fumyskin/TRIDANT_project/plots/batch1/GNSS_01.png

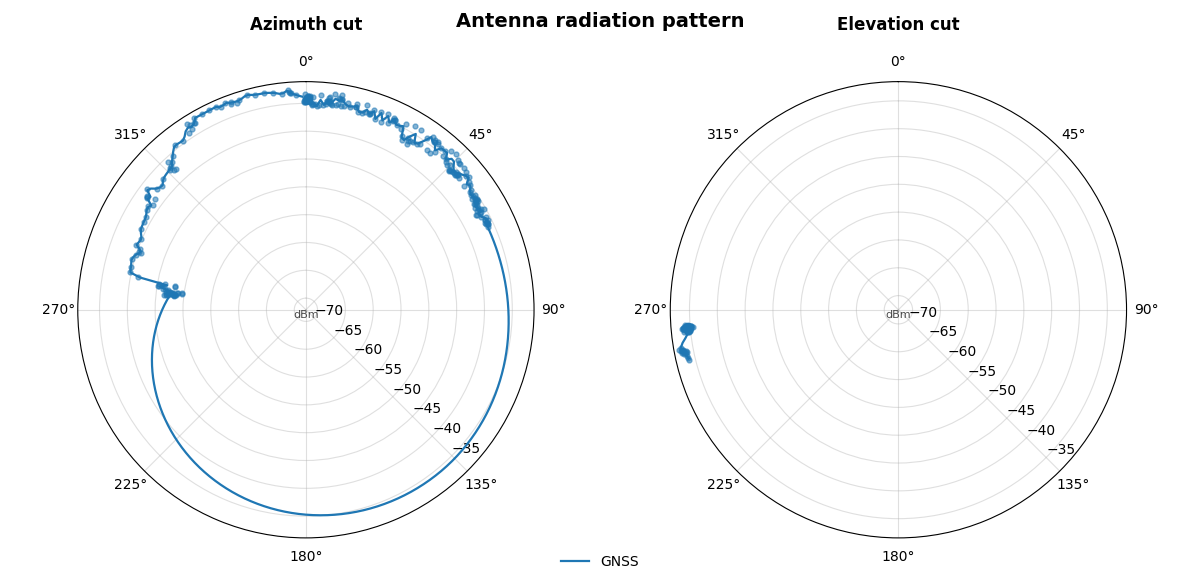
plots/batch1/GNSS_01.png
