fumyskin/TRIDANT_project/plots/batch1/GNSS_01_nhc.png

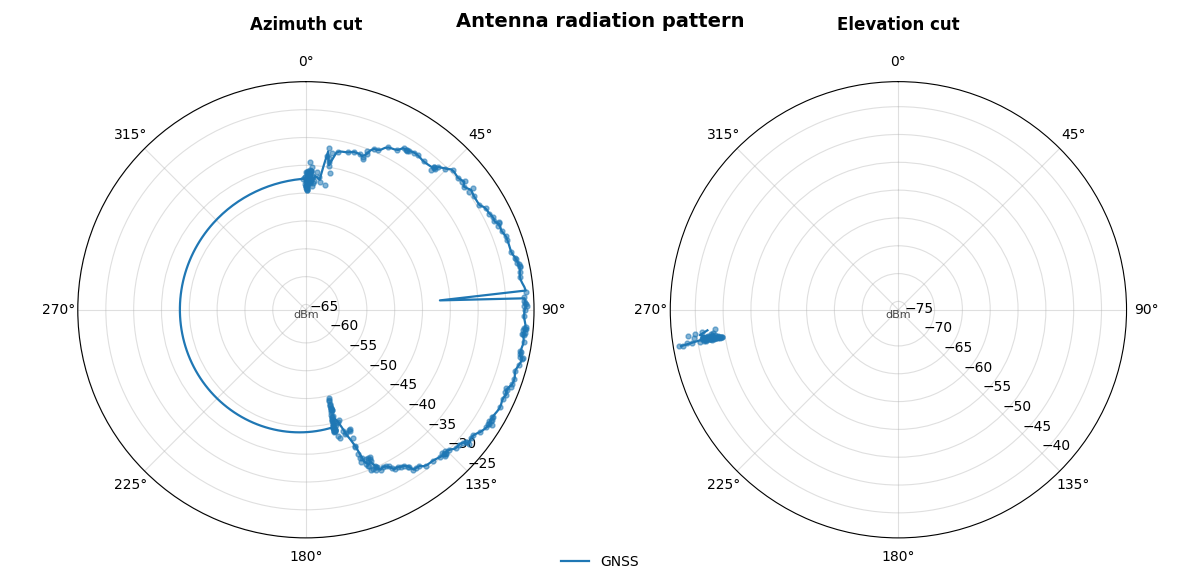
plots/batch1/GNSS_01_nhc.png
