fumyskin/TRIDANT_project/plots/batch1/GNSS_03_nhc_elevation.png

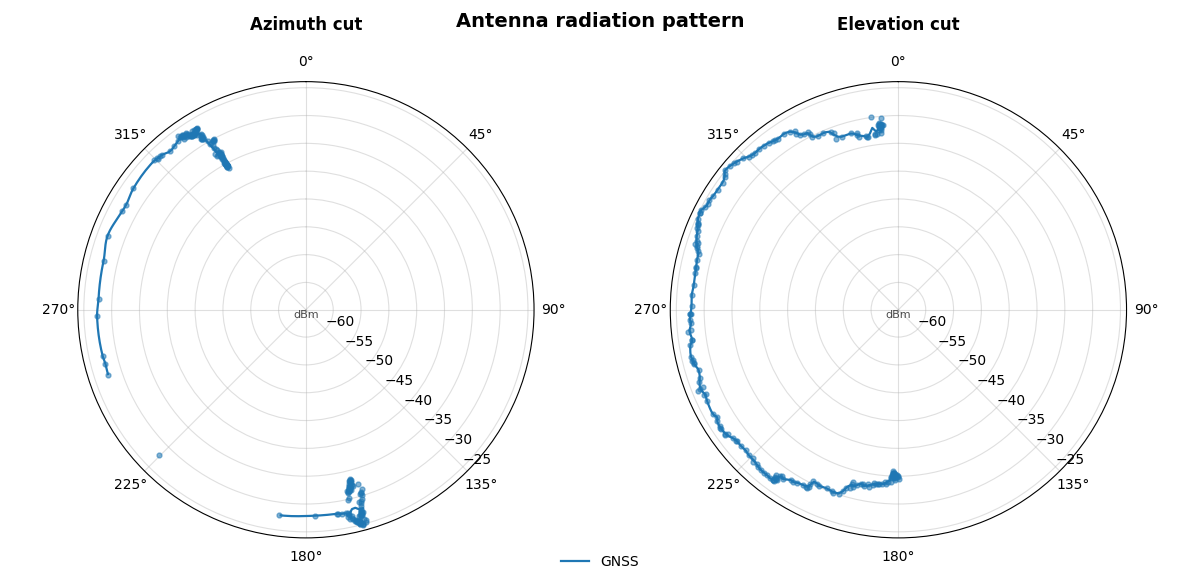
plots/batch1/GNSS_03_nhc_elevation.png
