fumyskin/TRIDANT_project/plots/batch1/V2X_01_elevation_half.png

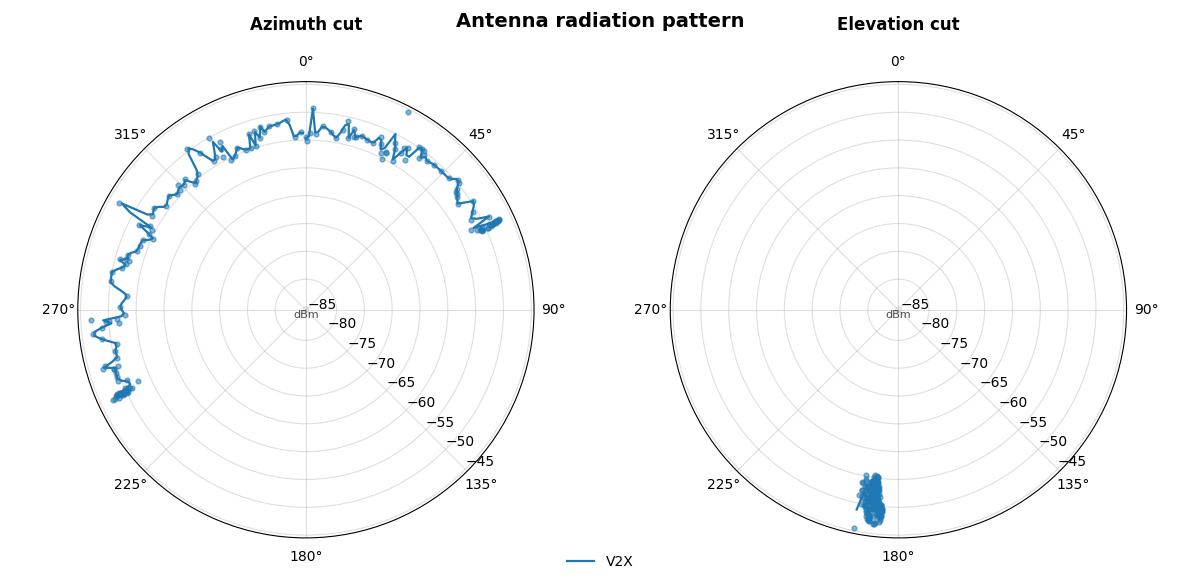
plots/batch1/V2X_01_elevation_half.png
