fumyskin/TRIDANT_project/plots/batch2/GNSS_01h.png

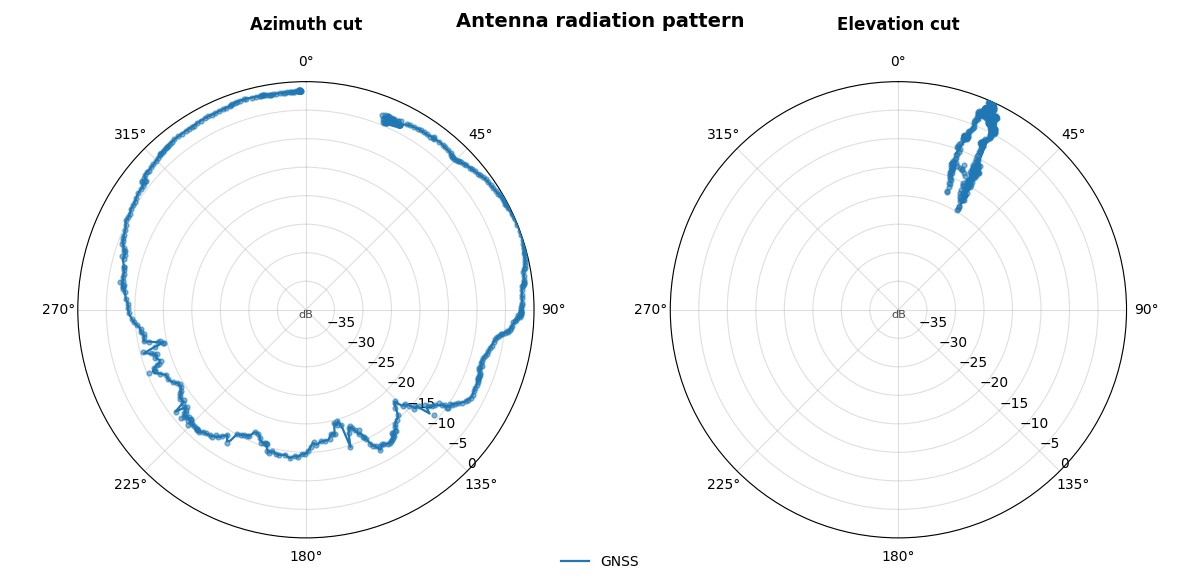
plots/batch2/GNSS_01h.png
