fumyskin/TRIDANT_project/plots/batch2/GNSS_01v.png

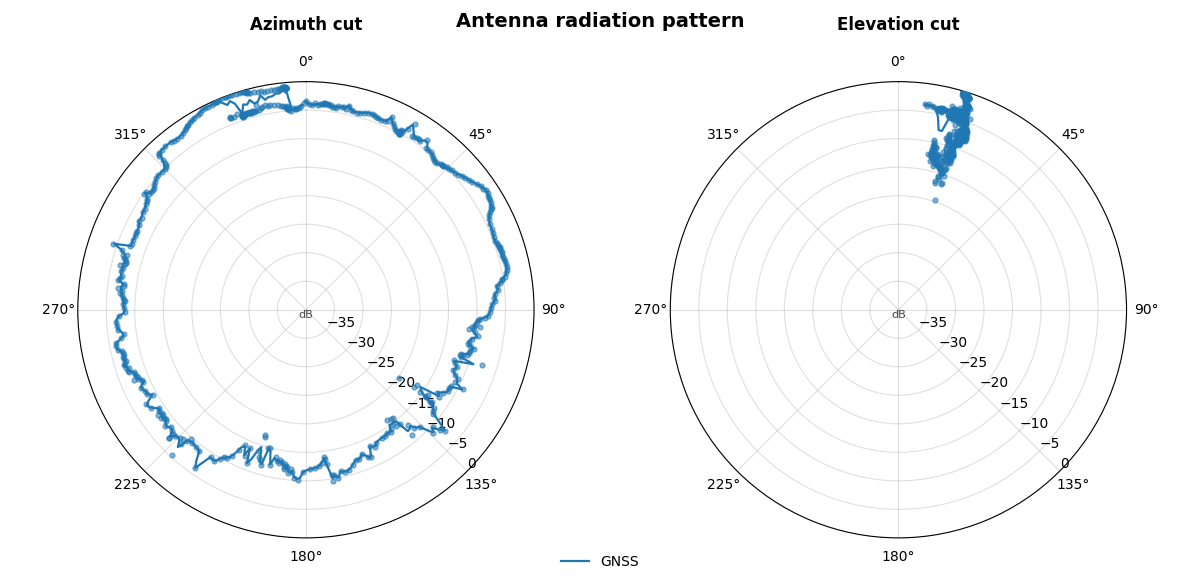
plots/batch2/GNSS_01v.png
