fumyskin/TRIDANT_project/plots/batch2/GNSS_03h.png

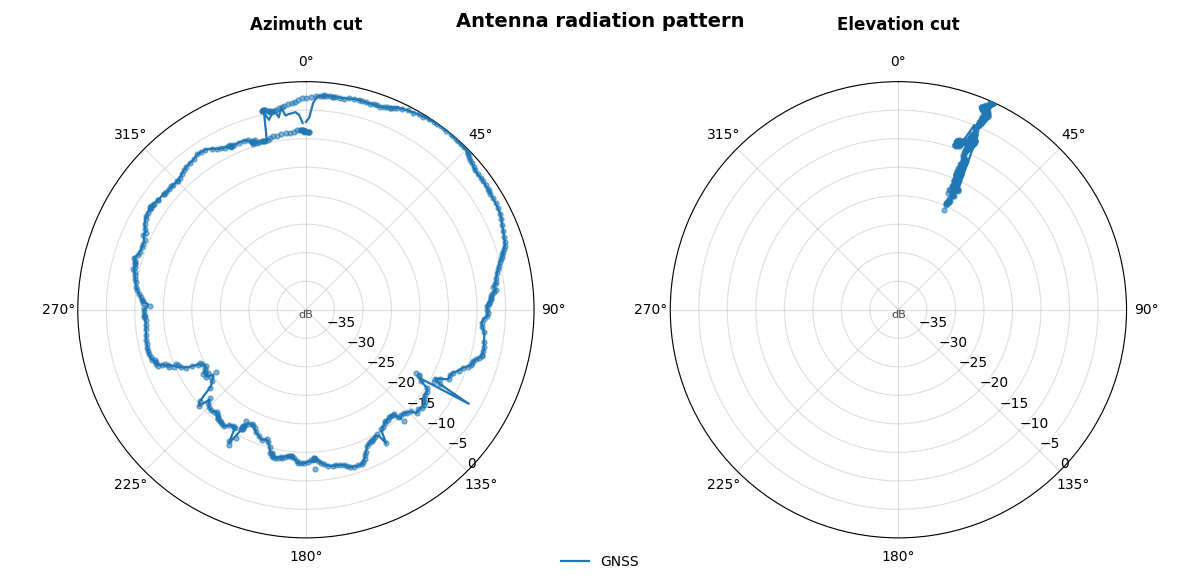
plots/batch2/GNSS_03h.png
