fumyskin/TRIDANT_project/plots/batch2/GNSS_04v.png

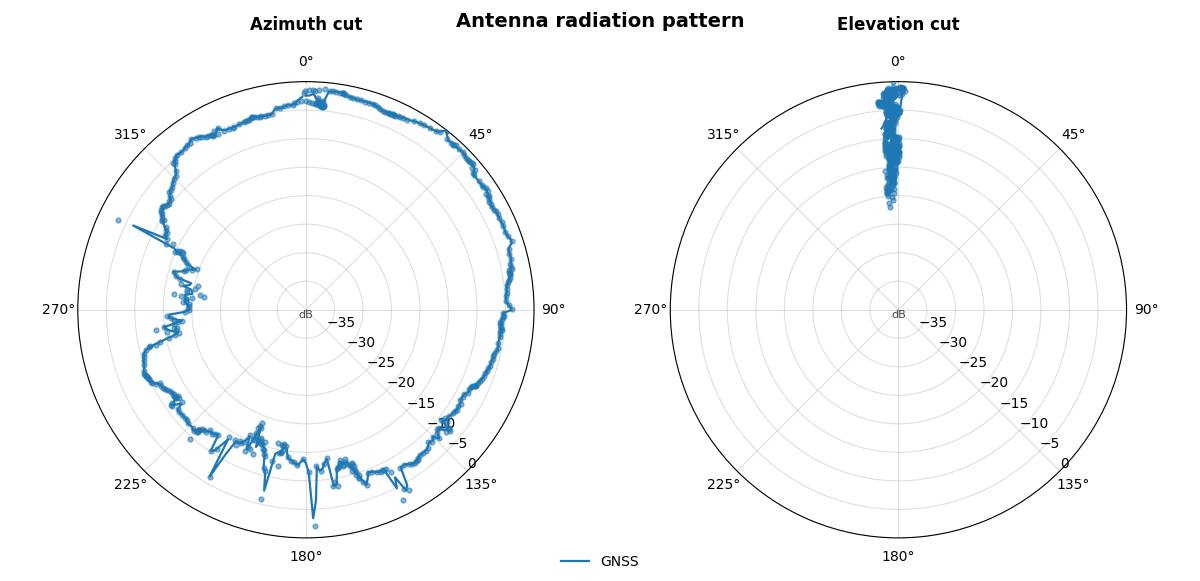
plots/batch2/GNSS_04v.png
