fumyskin/TRIDANT_project/plots/batch_final1.5/V2Xhcuth.png

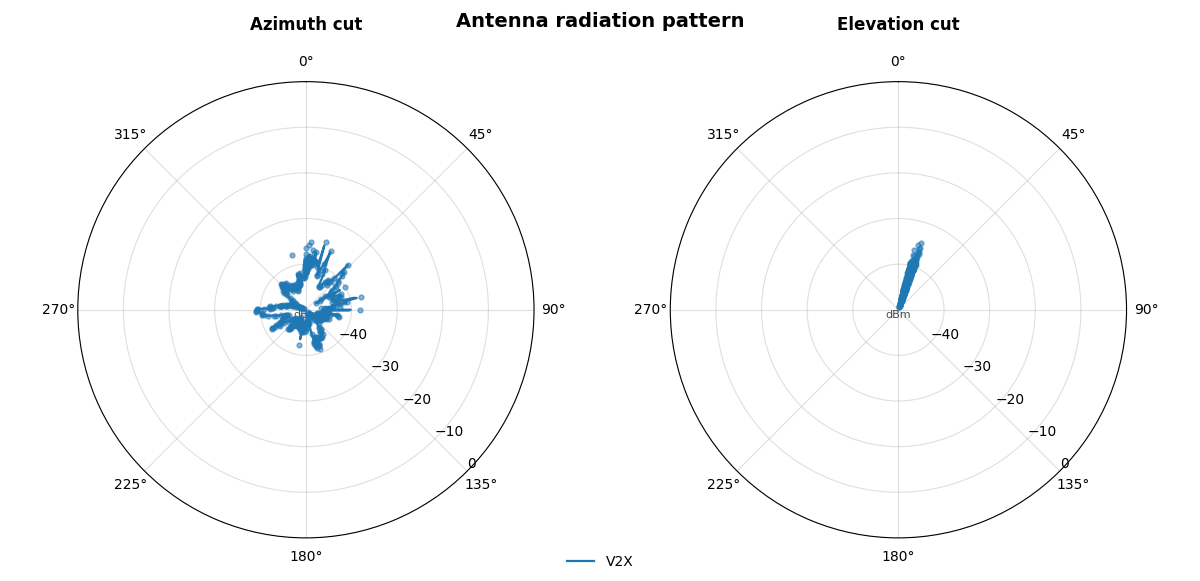
plots/batch_final1.5/V2Xhcuth.png
