fumyskin/TRIDANT_project/plots/batch_final2/V2X_01hcutv3x.png

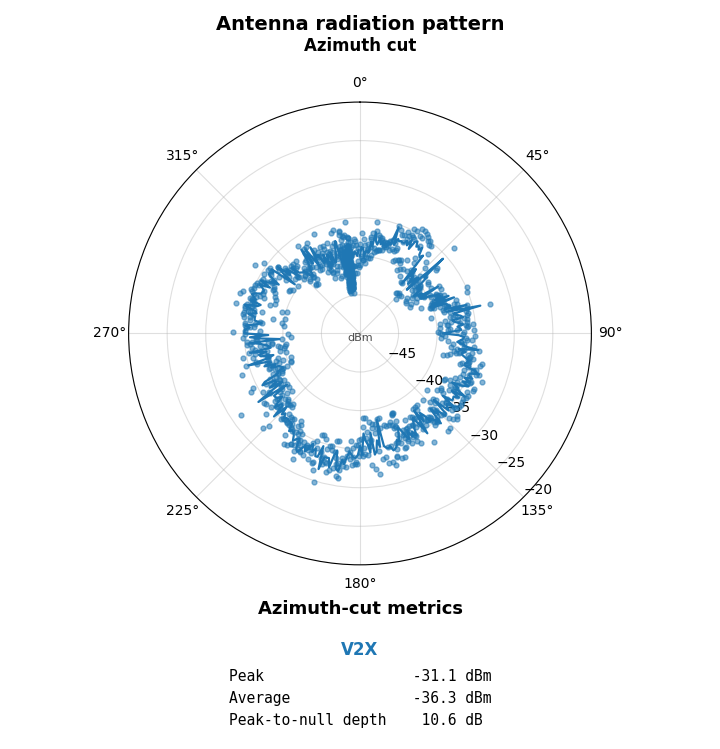
plots/batch_final2/V2X_01hcutv3x.png
