fumyskin/TRIDANT_project/plots/batch_final/GNSS_06hcut.png

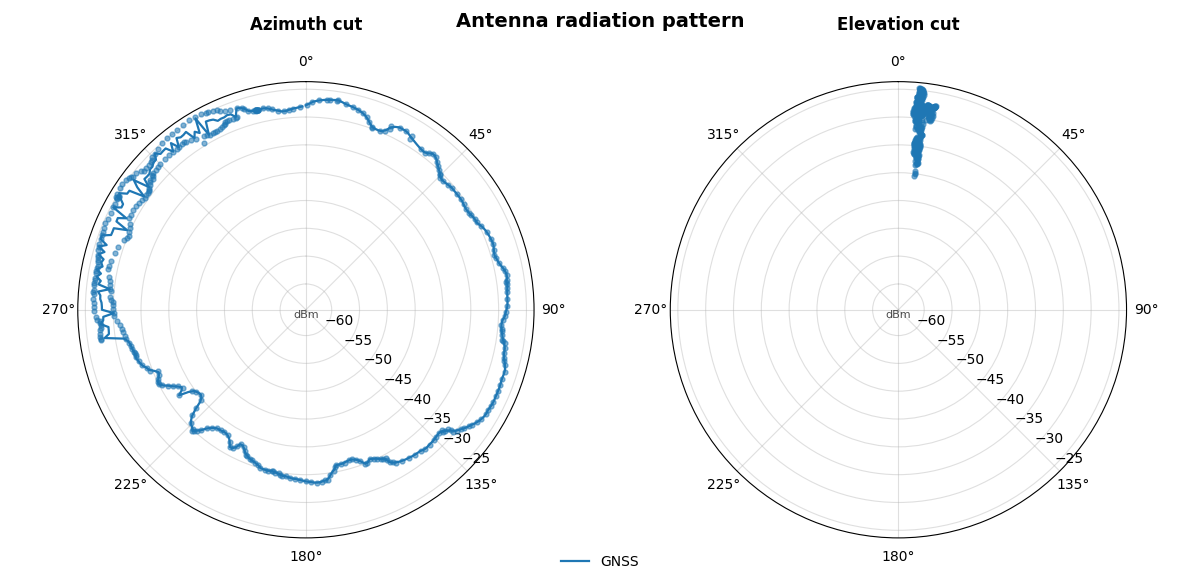
plots/batch_final/GNSS_06hcut.png
