fumyskin/TRIDANT_project/plots/batch_final/V2X_06hcutv1.png

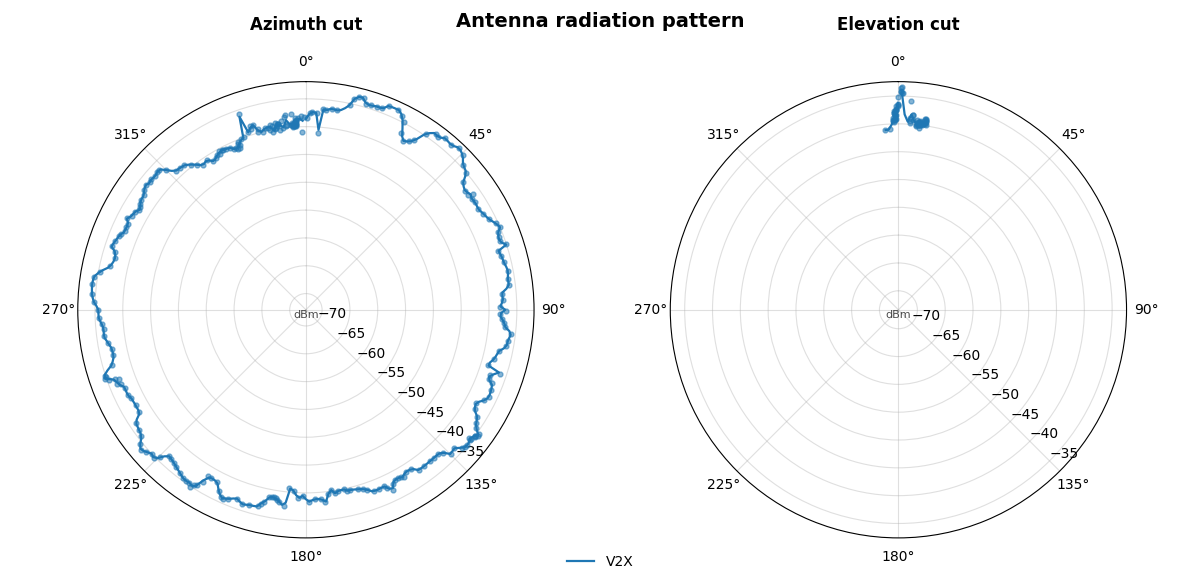
plots/batch_final/V2X_06hcutv1.png
