fumyskin/TRIDANT_project/plots/batch_final/V2X_06hcutv.png

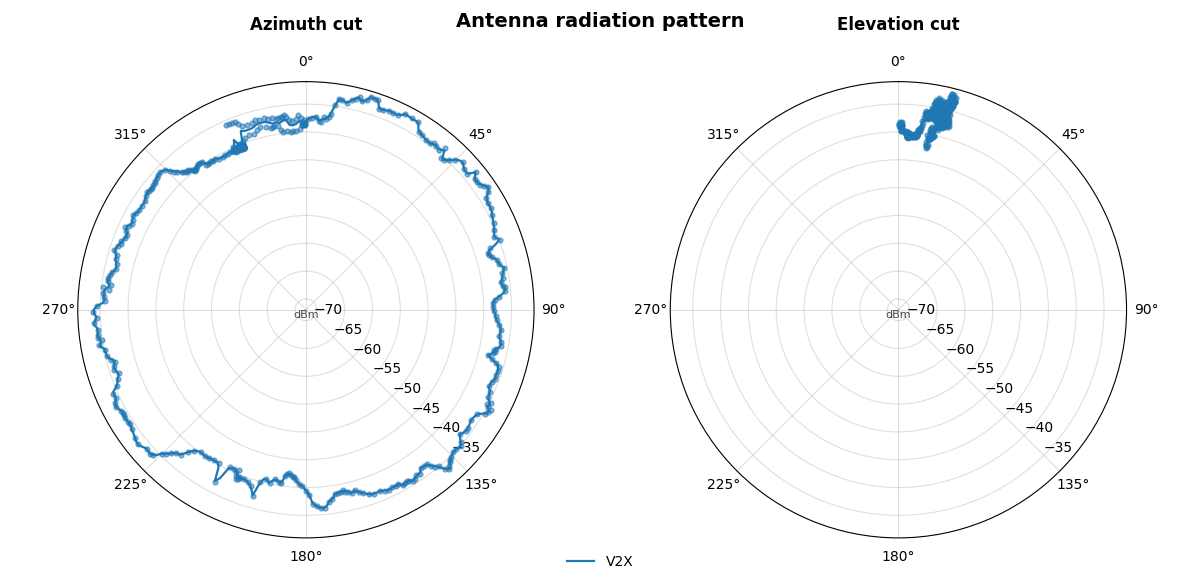
plots/batch_final/V2X_06hcutv.png
