fumyskin/TRIDANT_project/plots/batch_final/V2X_06vcutvfinal.png

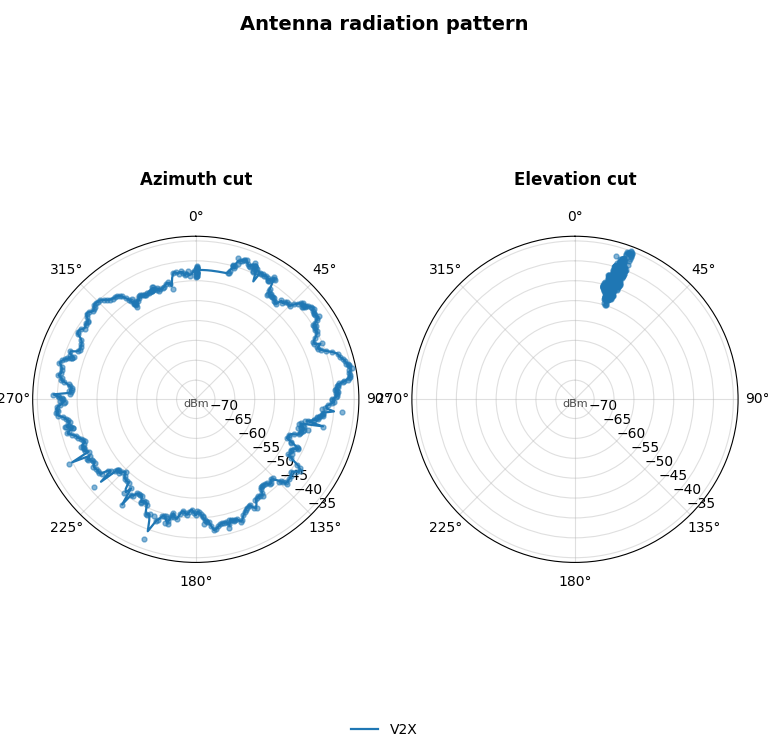
plots/batch_final/V2X_06vcutvfinal.png
